PolybotRiviera/polymartien/organization/Gantt_planning.png

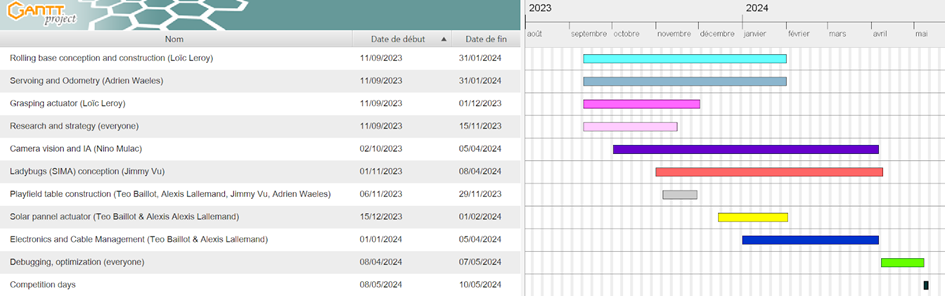
organization/Gantt_planning.png
