PolybotRiviera/polymartien/reports/Adrien's Reports/Report's images/Session03/code_interrupt_function_leftEncoder.png

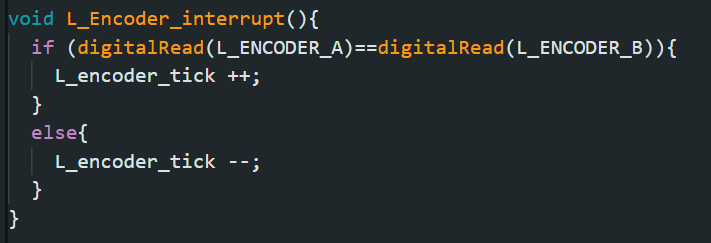
reports/Adrien's Reports/Report's images/Session03/code_interrupt_function_leftEncoder.png
