PolybotRiviera/polymartien/reports/Adrien's Reports/Report's images/Session07/Cutted_motor_shaft.jpg

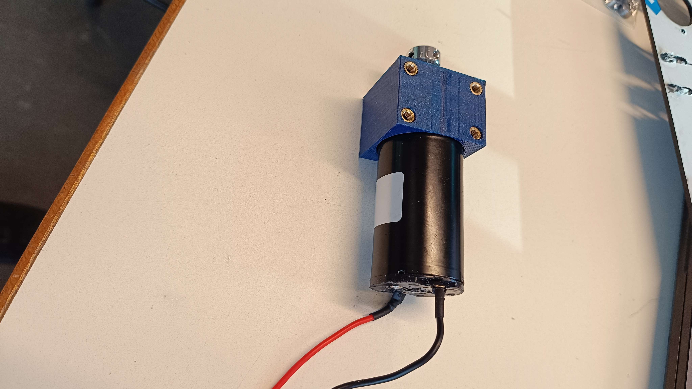
reports/Adrien's Reports/Report's images/Session07/Cutted_motor_shaft.jpg
