PolybotRiviera/polymartien/reports/Adrien's Reports/Report's images/Session07/inserts_newMotorSupports.jpg

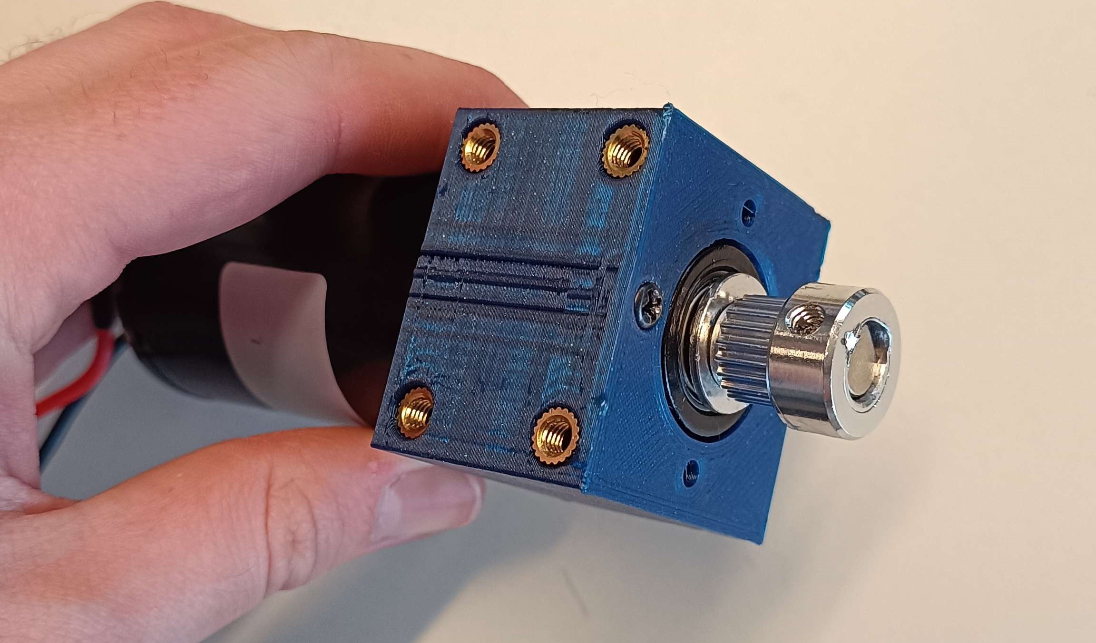
reports/Adrien's Reports/Report's images/Session07/inserts_newMotorSupports.jpg
