PolybotRiviera/polymartien/reports/Loïc's Reports/src/session_03/3d spring mount.jpg

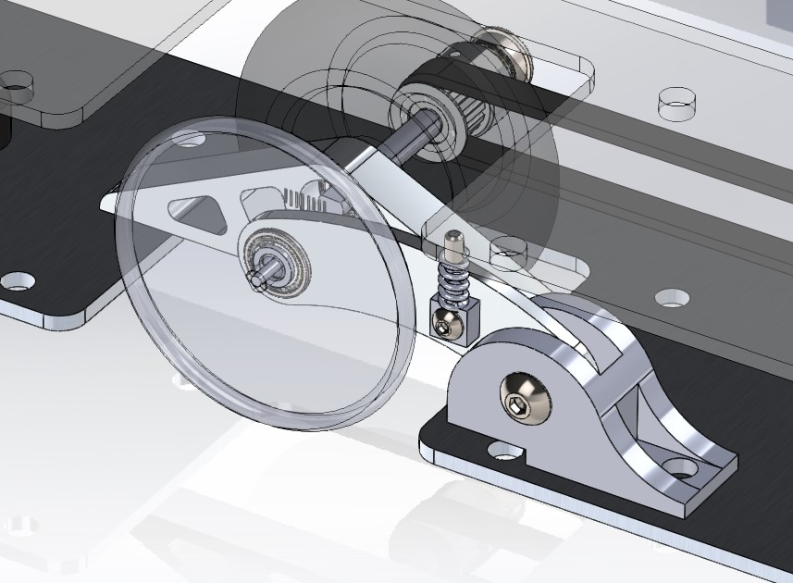
reports/Loïc's Reports/src/session_03/3d spring mount.jpg
