PolybotRiviera/polymartien/reports/Loïc's Reports/src/session_03/protection de roue 1.jpg

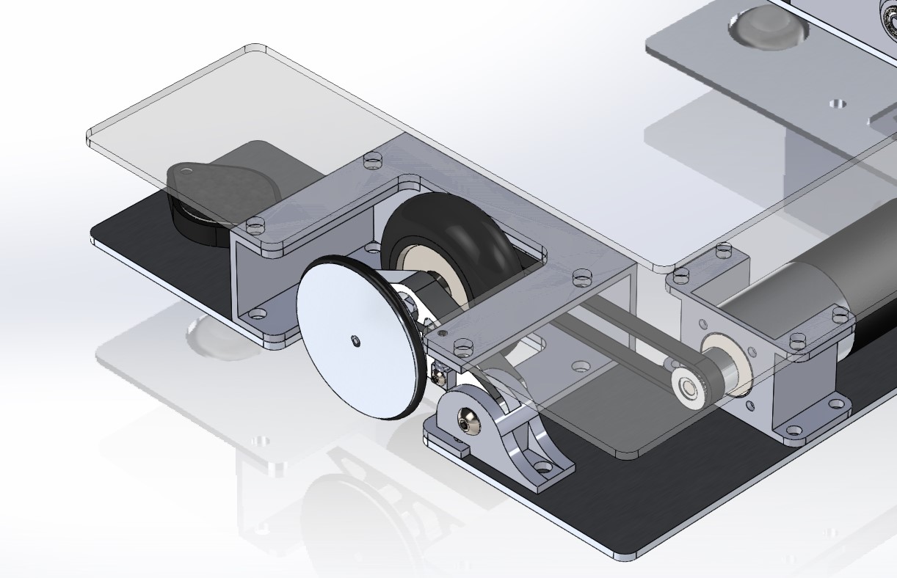
reports/Loïc's Reports/src/session_03/protection de roue 1.jpg
