PolybotRiviera/polymartien/reports/Loïc's Reports/src/session_03/protection de roue.jpg

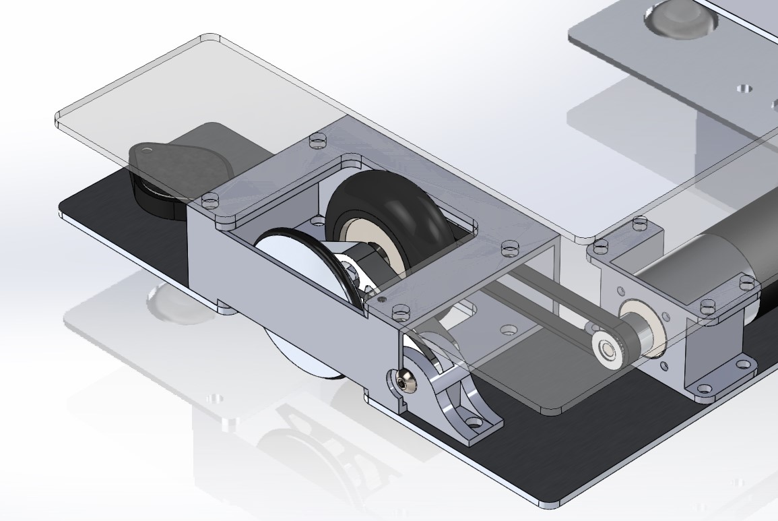
reports/Loïc's Reports/src/session_03/protection de roue.jpg
