PolybotRiviera/polymartien/reports/Loïc's Reports/src/session_03/spring mount.jpg

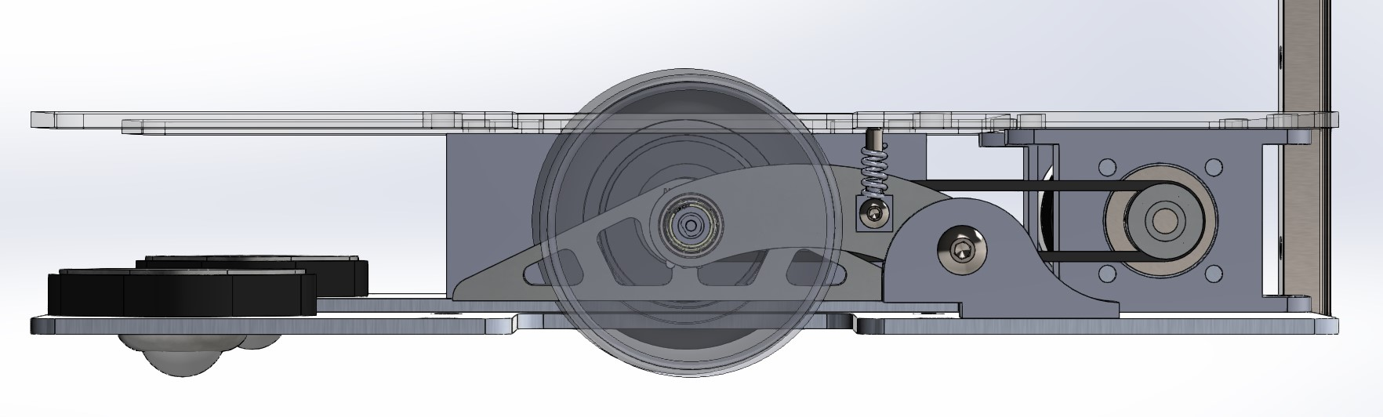
reports/Loïc's Reports/src/session_03/spring mount.jpg
