PolybotRiviera/polymartien/reports/Loïc's Reports/src/session_03/vue coupe pivot.jpg

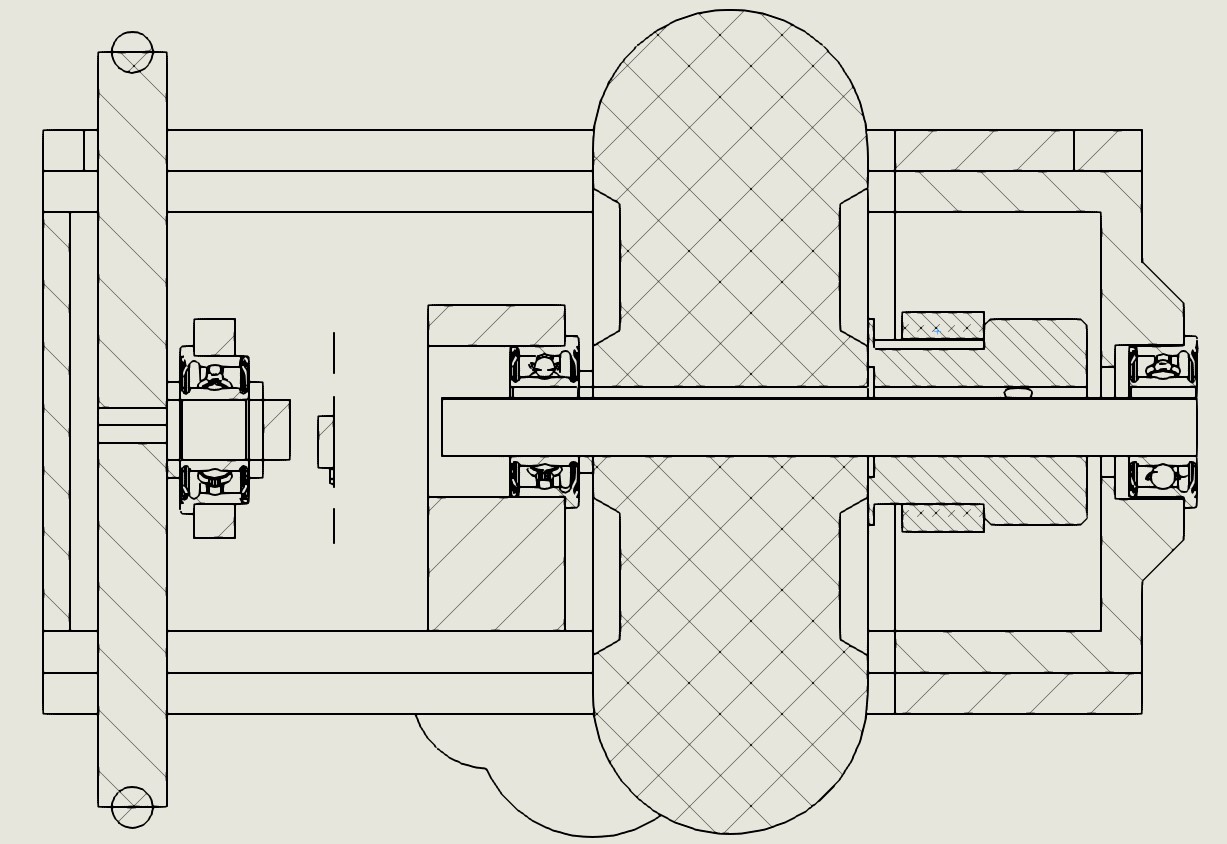
reports/Loïc's Reports/src/session_03/vue coupe pivot.jpg
