PolybotRiviera/polymartien/reports/Loïc's Reports/src/session_07/20240124_143823.jpg

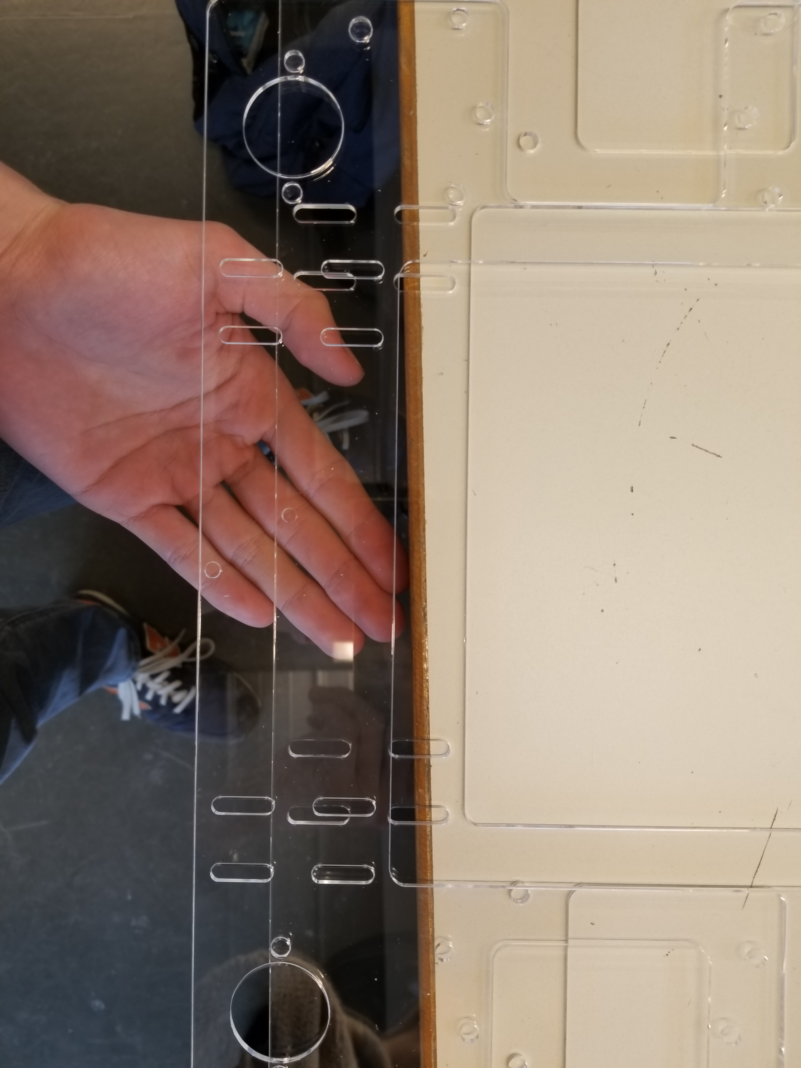
reports/Loïc's Reports/src/session_07/20240124_143823.jpg
