PolybotRiviera/polymartien/reports/Loïc's Reports/src/session_07/20240124_162406.jpg

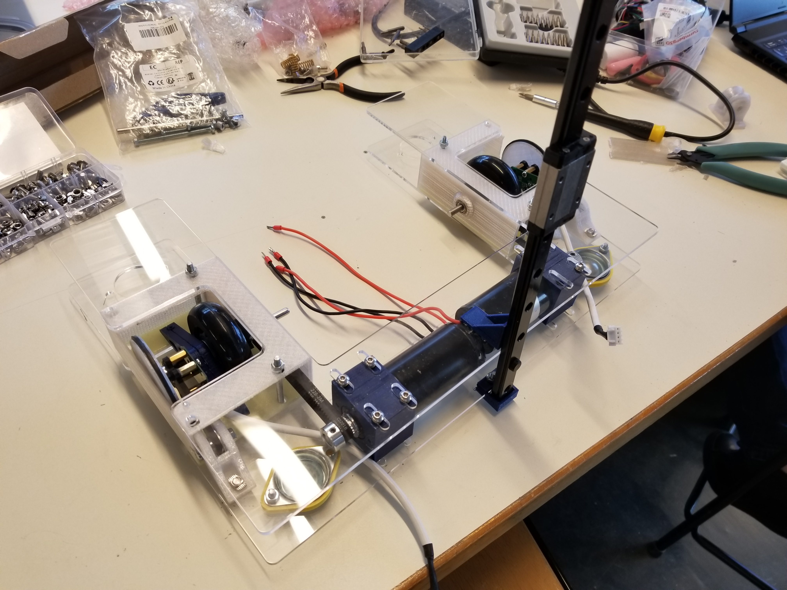
reports/Loïc's Reports/src/session_07/20240124_162406.jpg
