PolybotRiviera/polymartien/reports/Loïc's Reports/src/session_07/20240124_162414.jpg

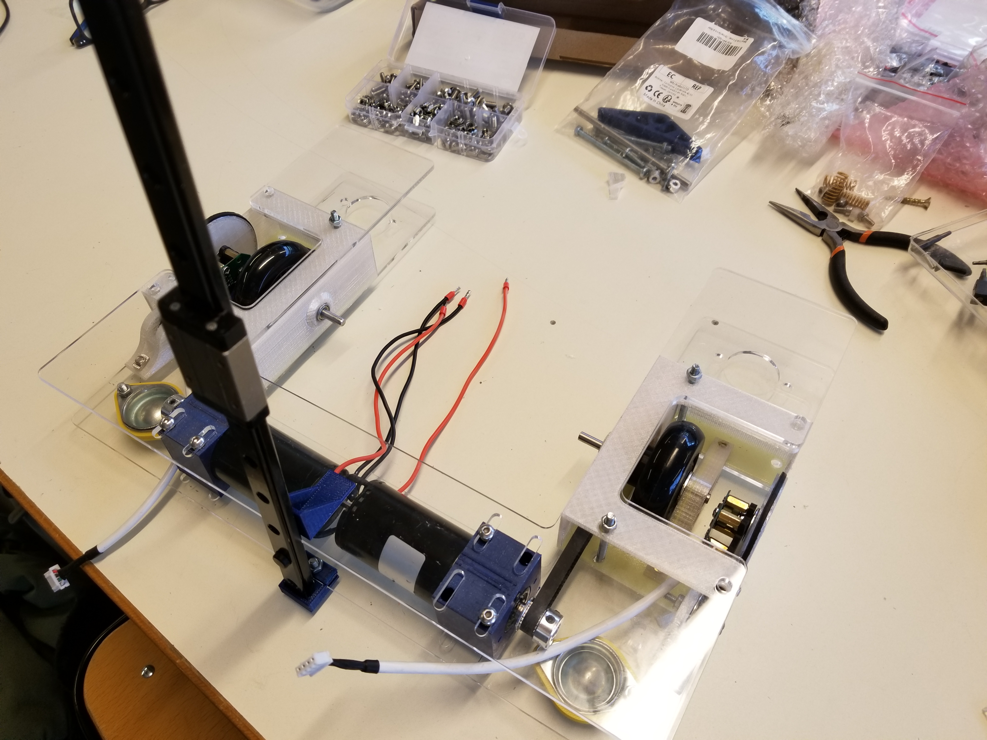
reports/Loïc's Reports/src/session_07/20240124_162414.jpg
