PolybotRiviera/polymartien/reports/Loïc's Reports/src/session_07/20240124_163049.jpg

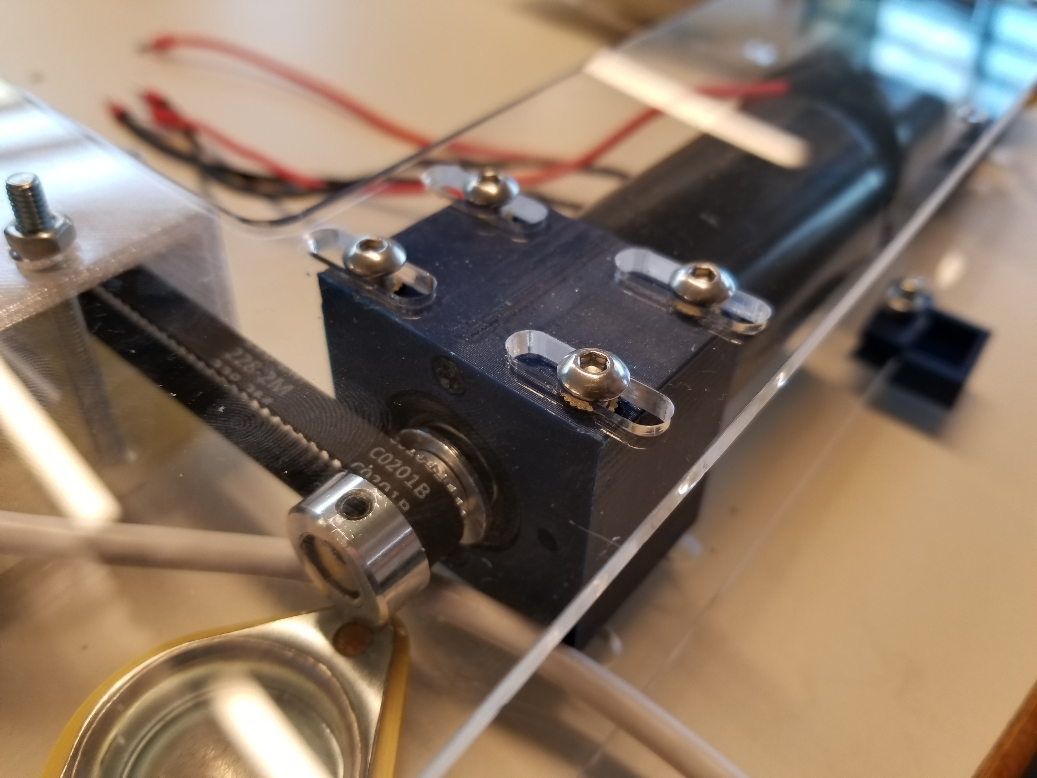
reports/Loïc's Reports/src/session_07/20240124_163049.jpg
