PolybotRiviera/polymartien/reports/Loïc's Reports/src/session_07/20240124_163106.jpg

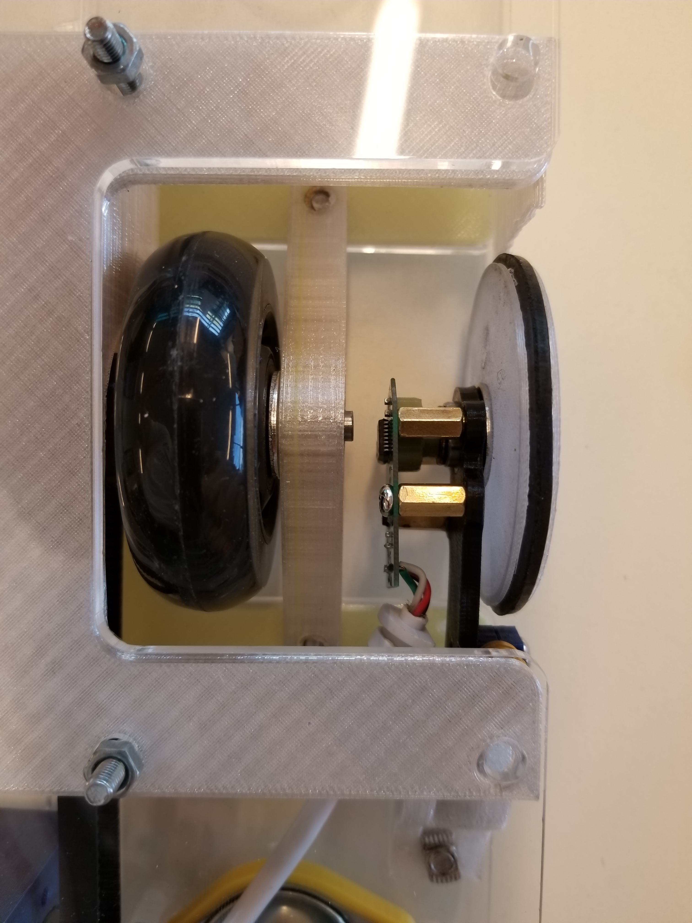
reports/Loïc's Reports/src/session_07/20240124_163106.jpg
