PolybotRiviera/polymartien/reports/Loïc's Reports/src/session_08/20240206_105811.jpg

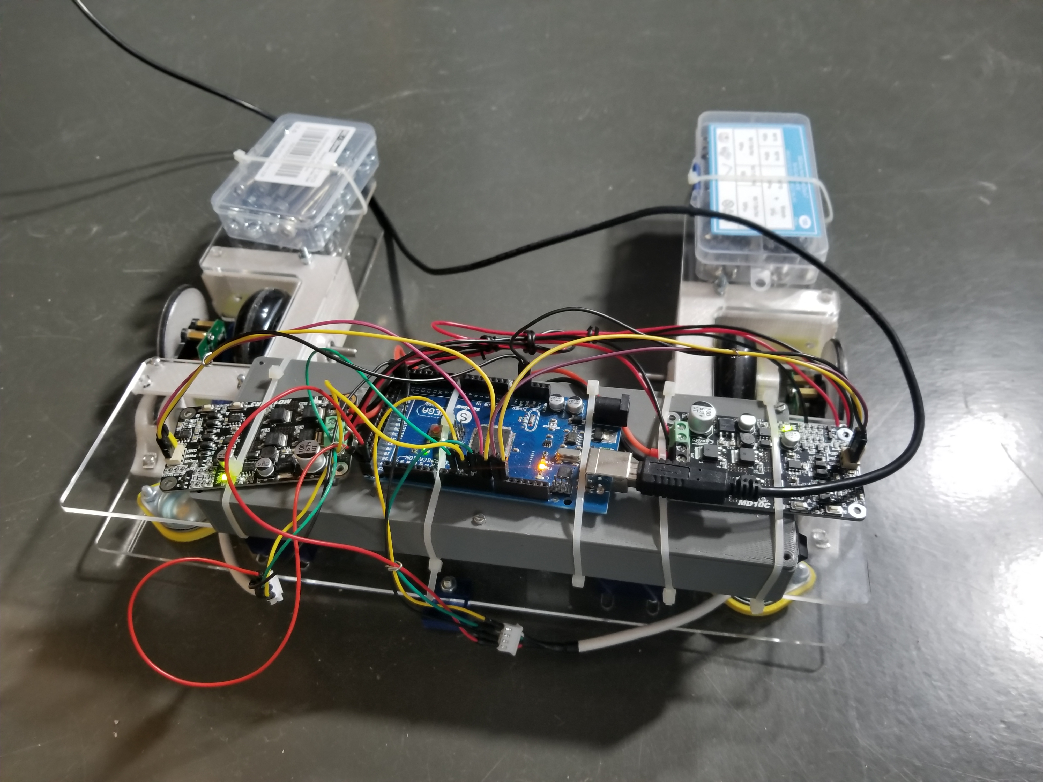
reports/Loïc's Reports/src/session_08/20240206_105811.jpg
