PolybotRiviera/polymartien/reports/Loïc's Reports/src/session_08/20240207_143602.jpg

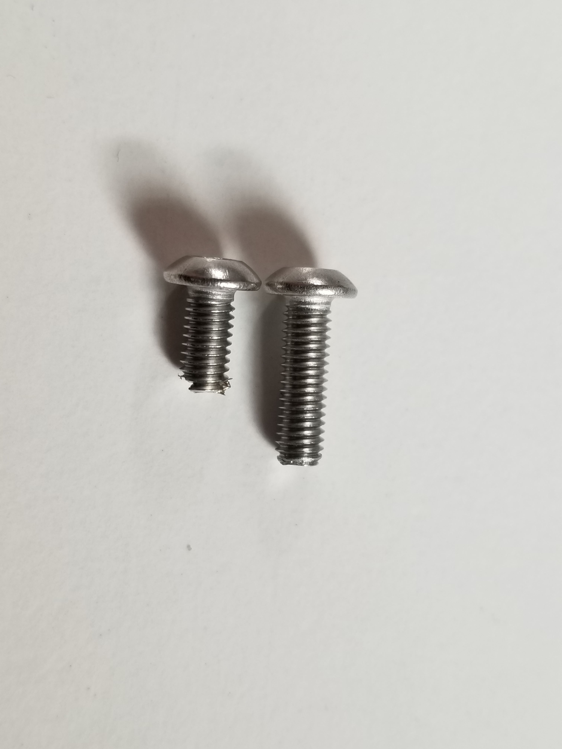
reports/Loïc's Reports/src/session_08/20240207_143602.jpg
