PolybotRiviera/polymartien/reports/Loïc's Reports/src/session_08/20240207_181306.jpg

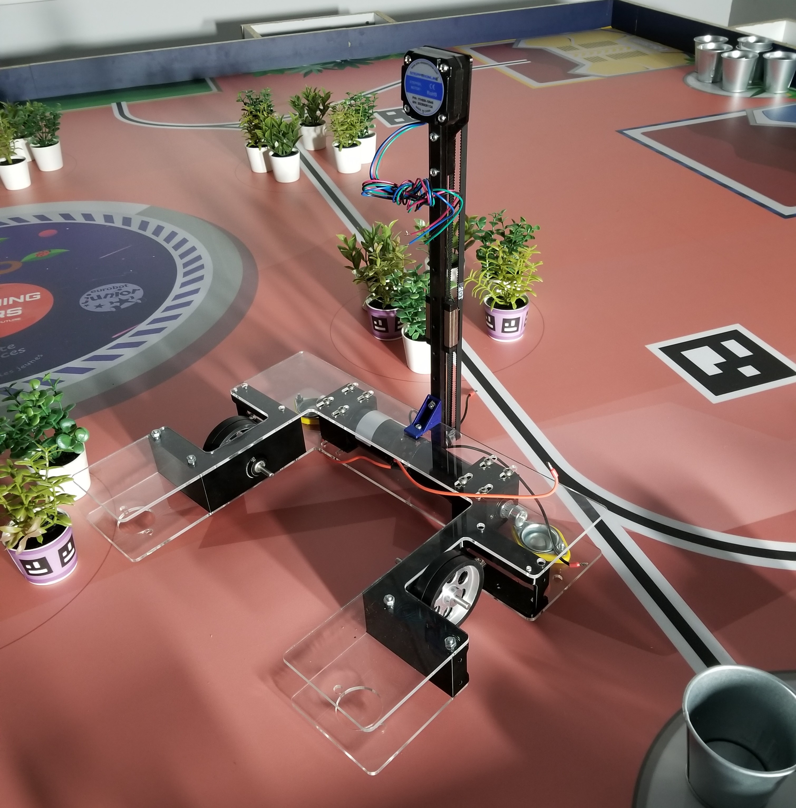
reports/Loïc's Reports/src/session_08/20240207_181306.jpg
