PolybotRiviera/polymartien/reports/Loïc's Reports/src/session_09/20240207_145429.jpg

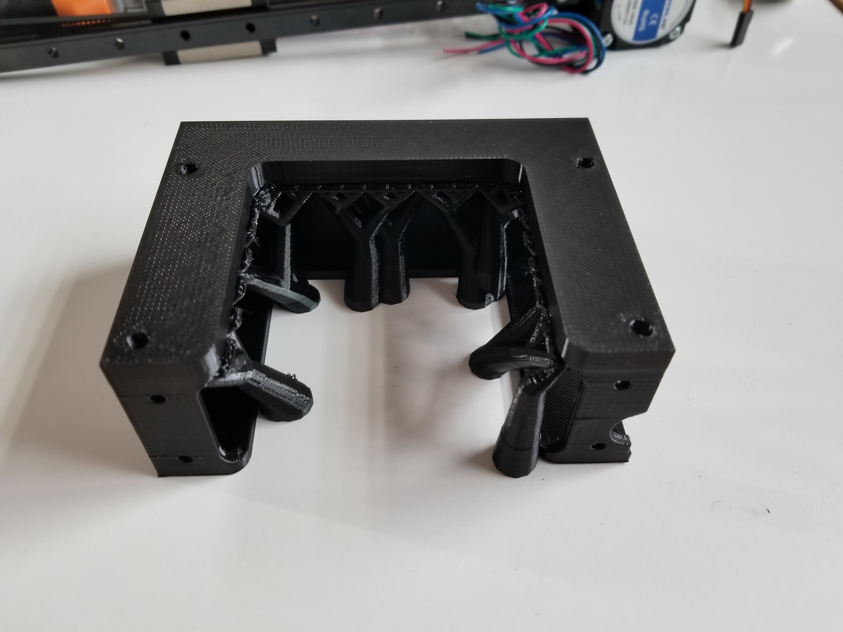
reports/Loïc's Reports/src/session_09/20240207_145429.jpg
