PolybotRiviera/polymartien/reports/Loïc's Reports/src/session_09/20240207_145442.jpg

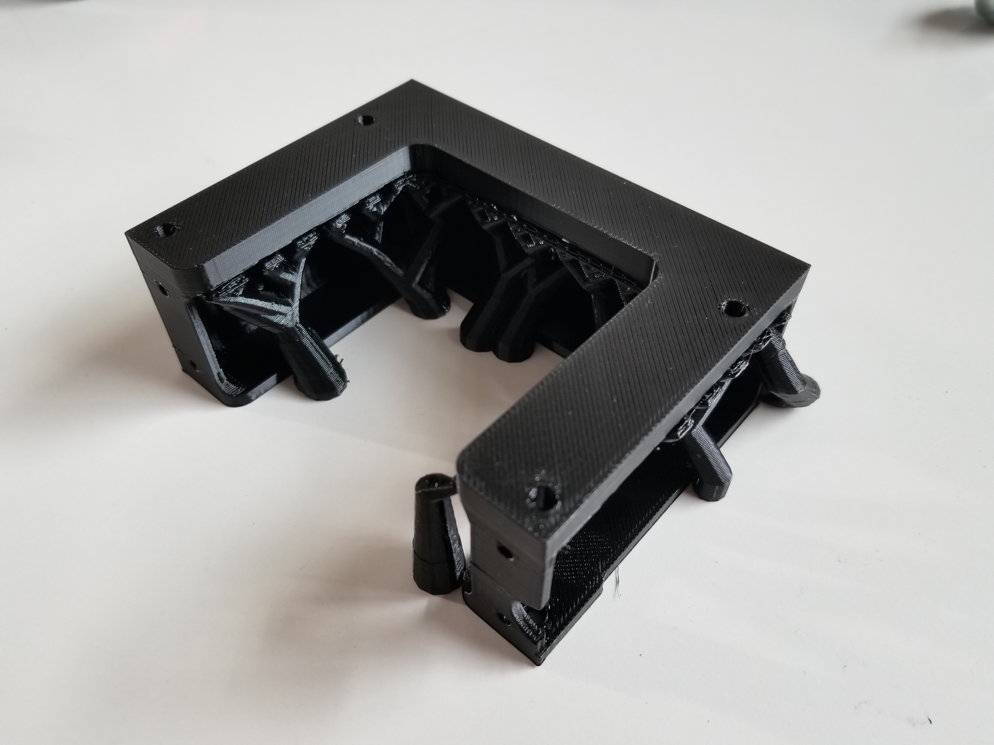
reports/Loïc's Reports/src/session_09/20240207_145442.jpg
