PolybotRiviera/polymartien/reports/Loïc's Reports/src/session_09/20240207_145531.jpg

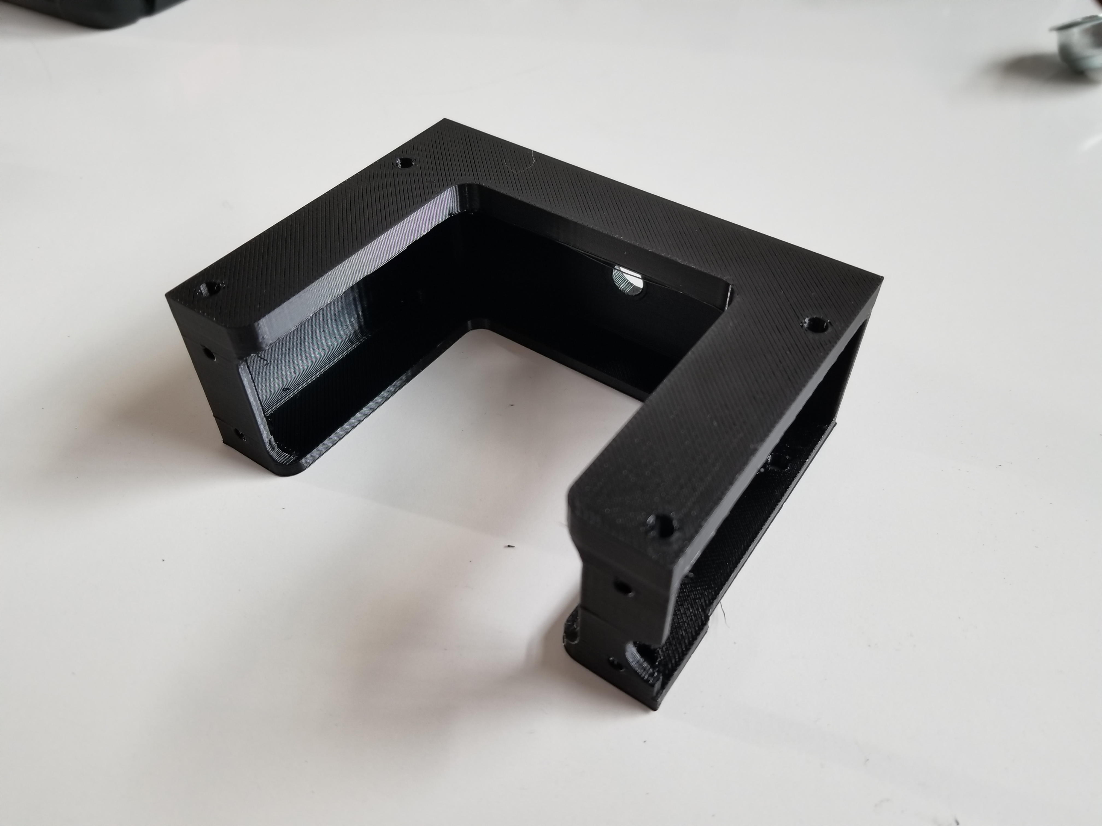
reports/Loïc's Reports/src/session_09/20240207_145531.jpg
