PolybotRiviera/polymartien/src/farming mars.png

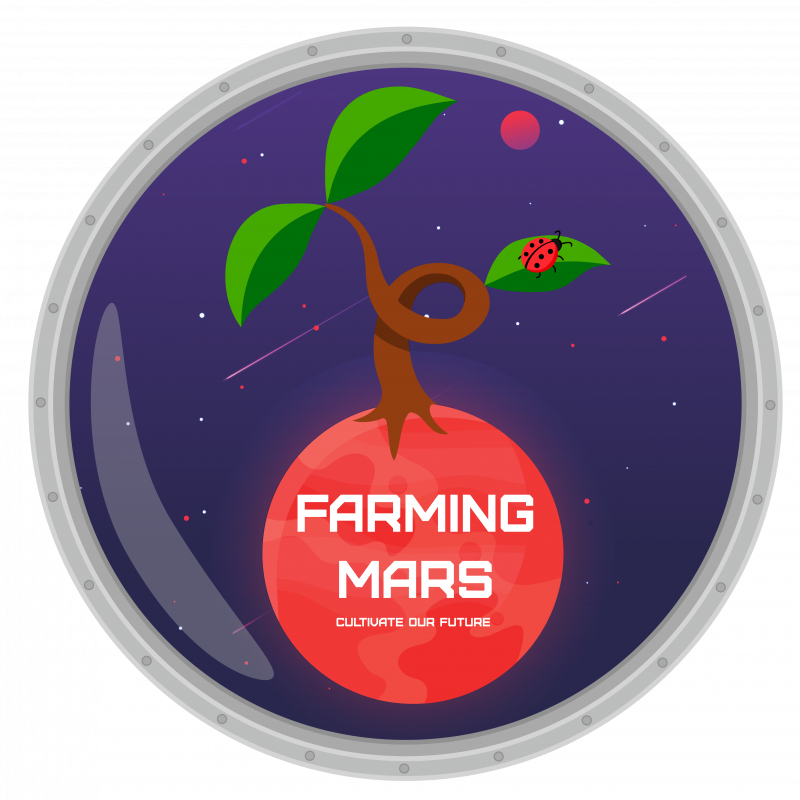
src/farming mars.png
