PolybotRiviera/polymartien/reports/Loïc's Reports/src/session_07/3d printing2.jpg

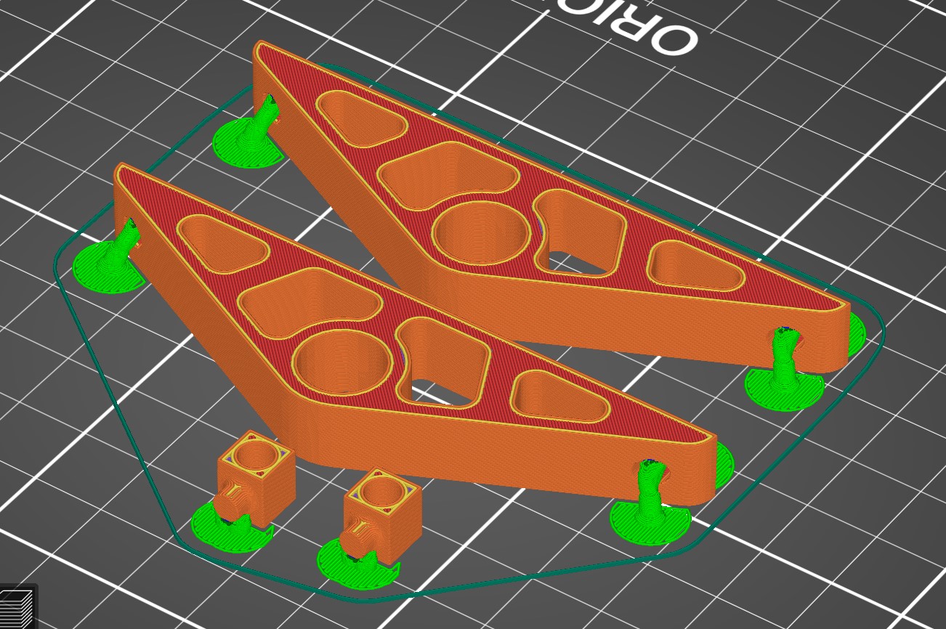
reports/Loïc's Reports/src/session_07/3d printing2.jpg
