PolybotRiviera/polymartien/reports/Loïc's Reports/src/session_09/grabber assembled.jpeg

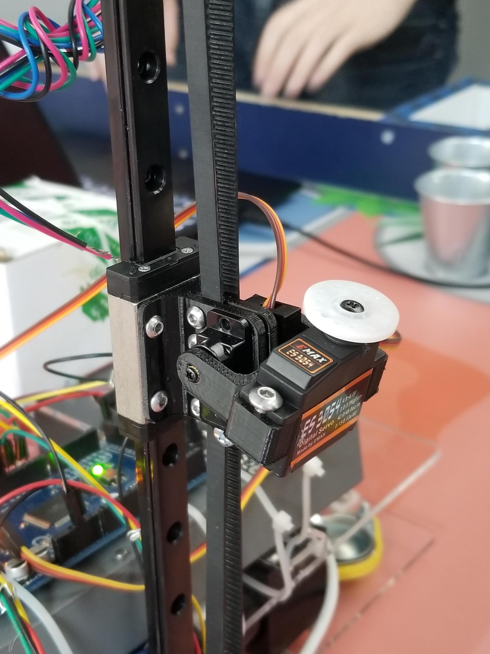
reports/Loïc's Reports/src/session_09/grabber assembled.jpeg
