PolybotRiviera/polymartien/software/riviera/bot/communication_codes.py

"""
Module saving the codes for every action.
"""

START = 0xff-1

EMERGENCY_STOP = 0xff-2
EMERGENCY_RESUME = 0xff-3

ROBOT_SPEED_LEFT = 0xff-4
ROBOT_SPEED_RIGHT = 0xff-5

GRABBER_HEIGHT = 0xff-6
GRABBER_ANGLE = 0xff-7

HOLDER_DISTANCE = 0xff-8
HOLDER_ANGLE = 0xff-9
