PolybotRiviera/polymartien/software/ladybug/led_test.py

import network
import socket
from time import sleep
import machine

ssid = "Bbox-5F909A4D"
password = "CkwgeRWW69nkULLYPn"

def connect():
    #Connect to WLAN
    wlan = network.WLAN(network.STA_IF)
    wlan.active(True)
    wlan.connect(ssid, password)
    while wlan.isconnected() == False:
        print('Waiting for connection...')
        sleep(1)
    ip = wlan.ifconfig()[0]
    print(f'Connected on {ip}')
    return ip


try:
    ip = connect()
except KeyboardInterrupt:
    machine.reset()
